t-manojkumar/ROBOTIC_ROVER/3D/Annotation ISO.png

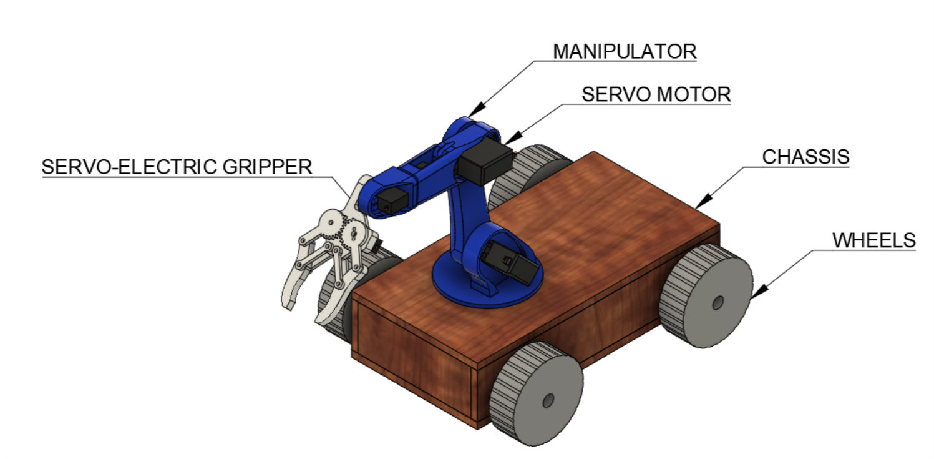
3D/Annotation ISO.png
