t-manojkumar/ROBOTIC_ROVER/3D/Annotation SIDE1.png

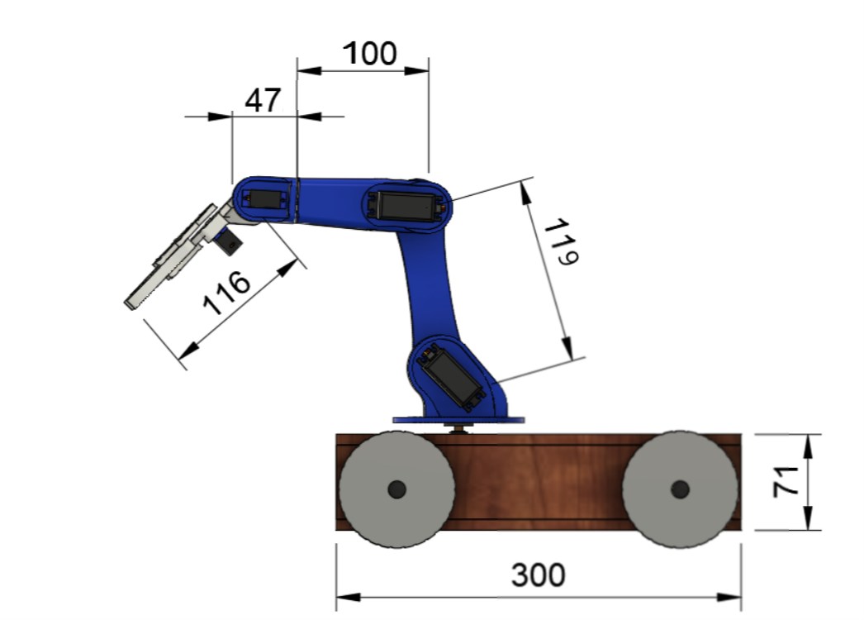
3D/Annotation SIDE1.png
