t-manojkumar/ROBOTIC_ROVER/3D/Annotation TOP.png

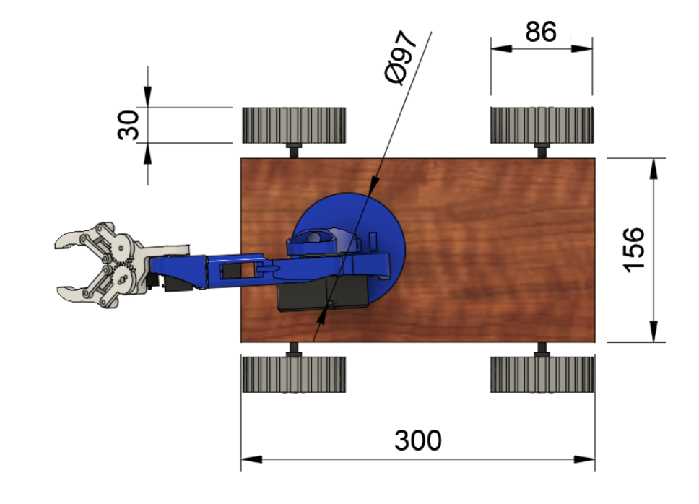
3D/Annotation TOP.png
