t-manojkumar/ROBOTIC_ROVER/CIRCUIT DIAGRAM/24d7c107-abdc-472a-8ade-f75f3b55037c.png

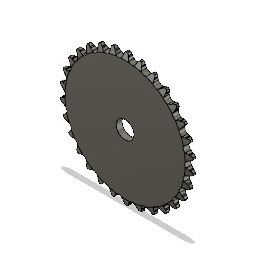
CIRCUIT DIAGRAM/24d7c107-abdc-472a-8ade-f75f3b55037c.png
