t-manojkumar/ROBOTIC_ROVER/CIRCUIT DIAGRAM/CIRCUIT.jpg

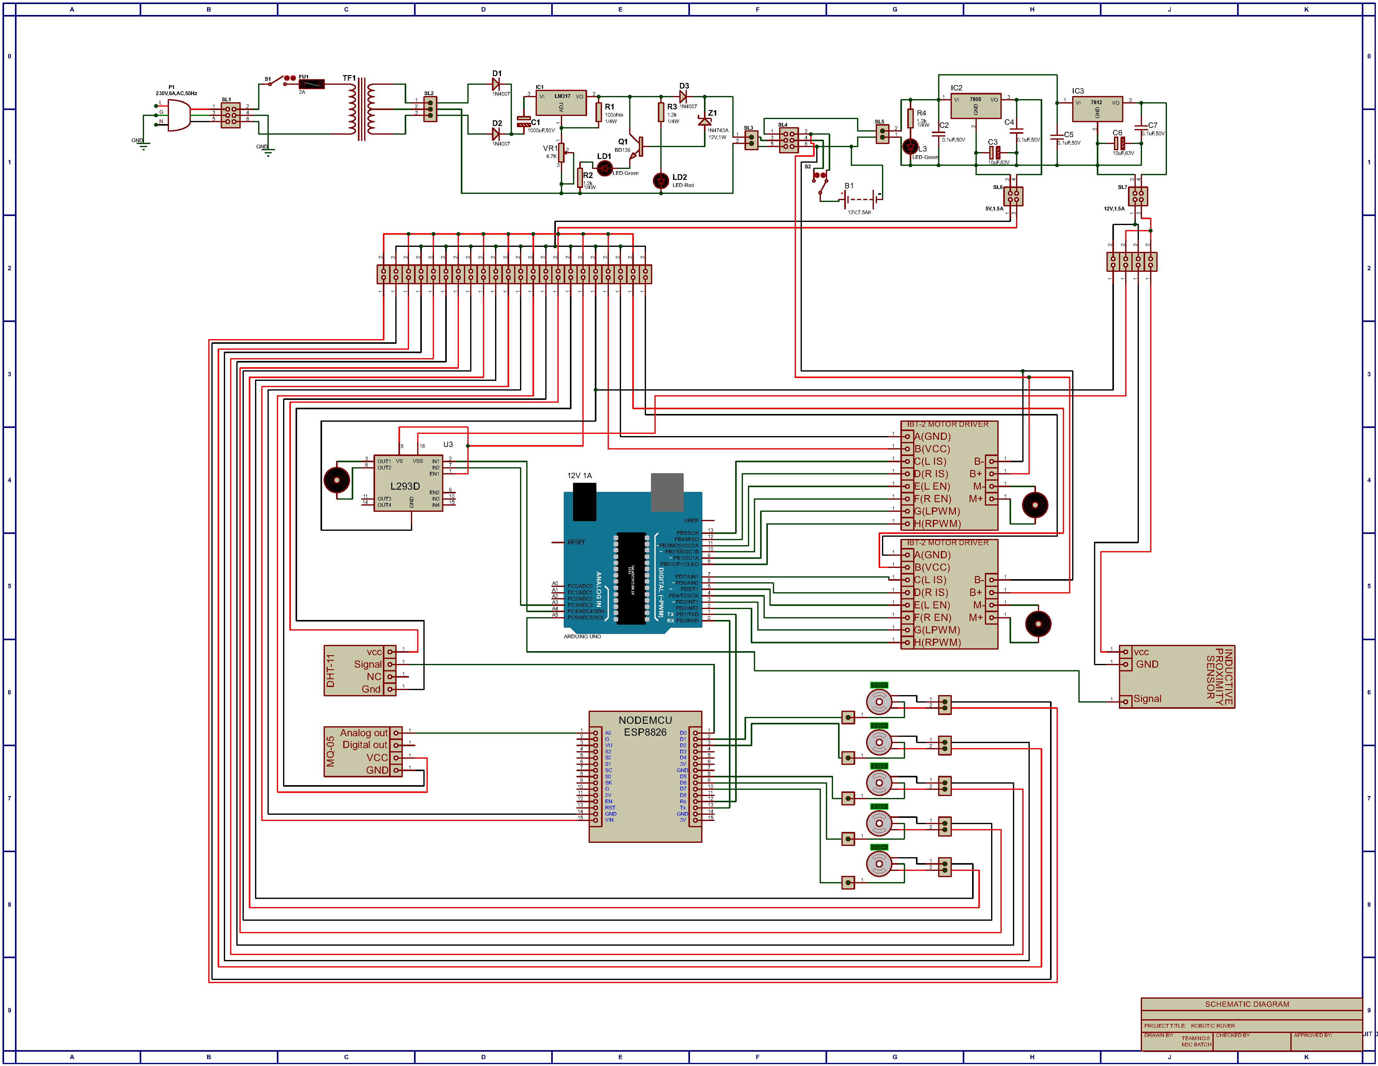
CIRCUIT DIAGRAM/CIRCUIT.jpg
