t-manojkumar/ROBOTIC_ROVER/MODULWISE/MODELWISE2.jpg

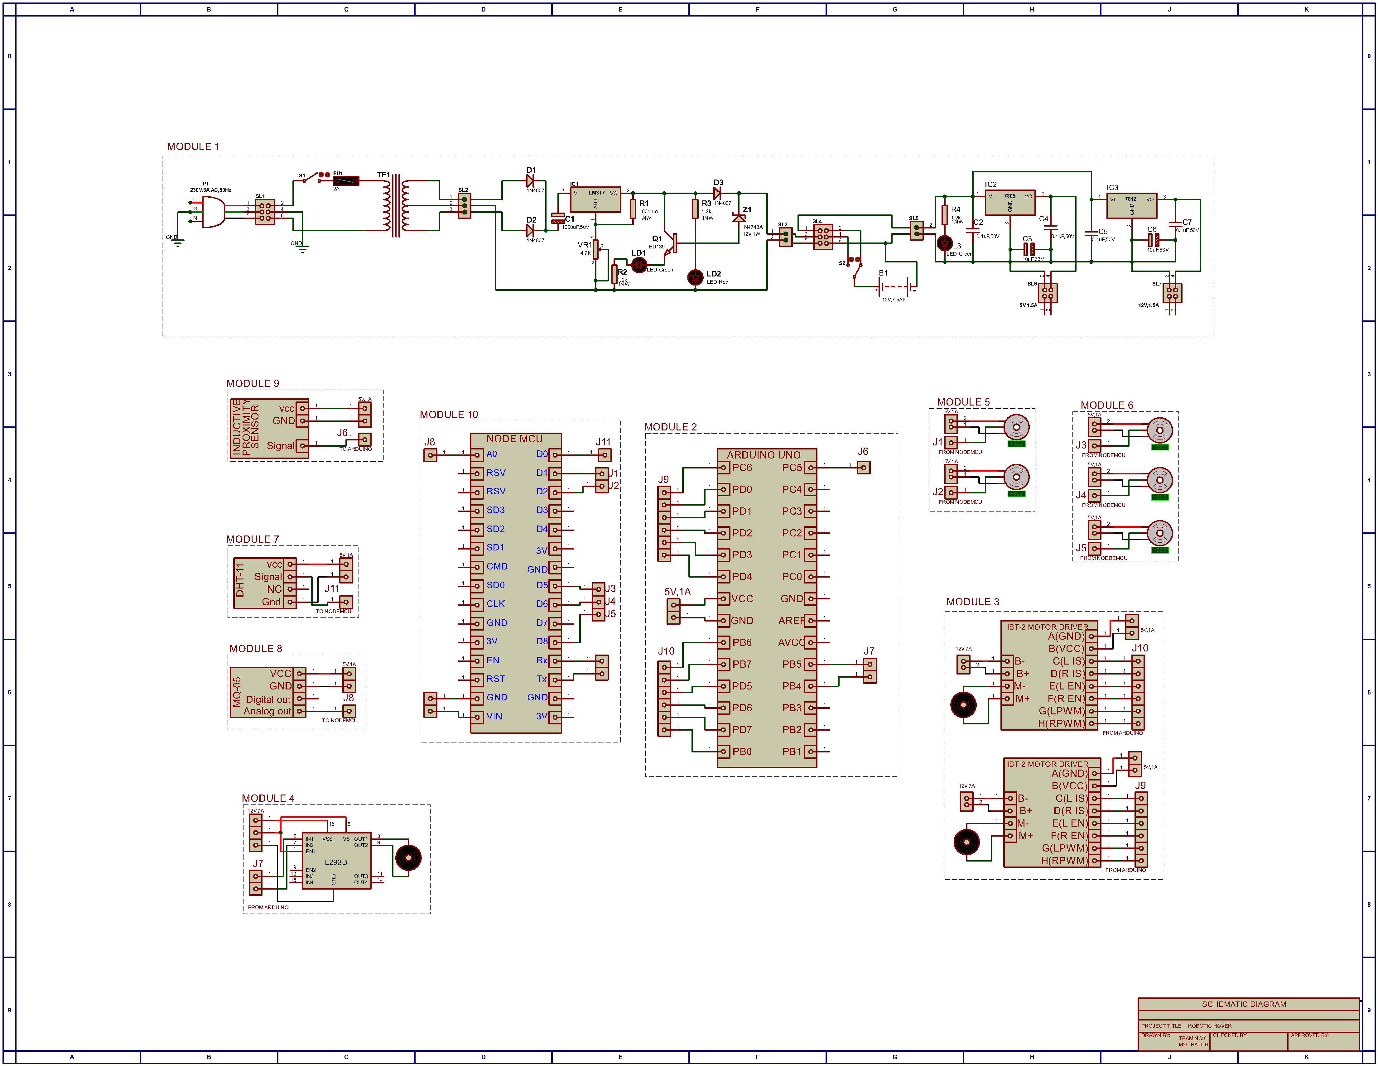
MODULWISE/MODELWISE2.jpg
