t-manojkumar/ROBOTIC_ROVER/MODULWISE/MODELWISE INTERCONNECTION.jpg

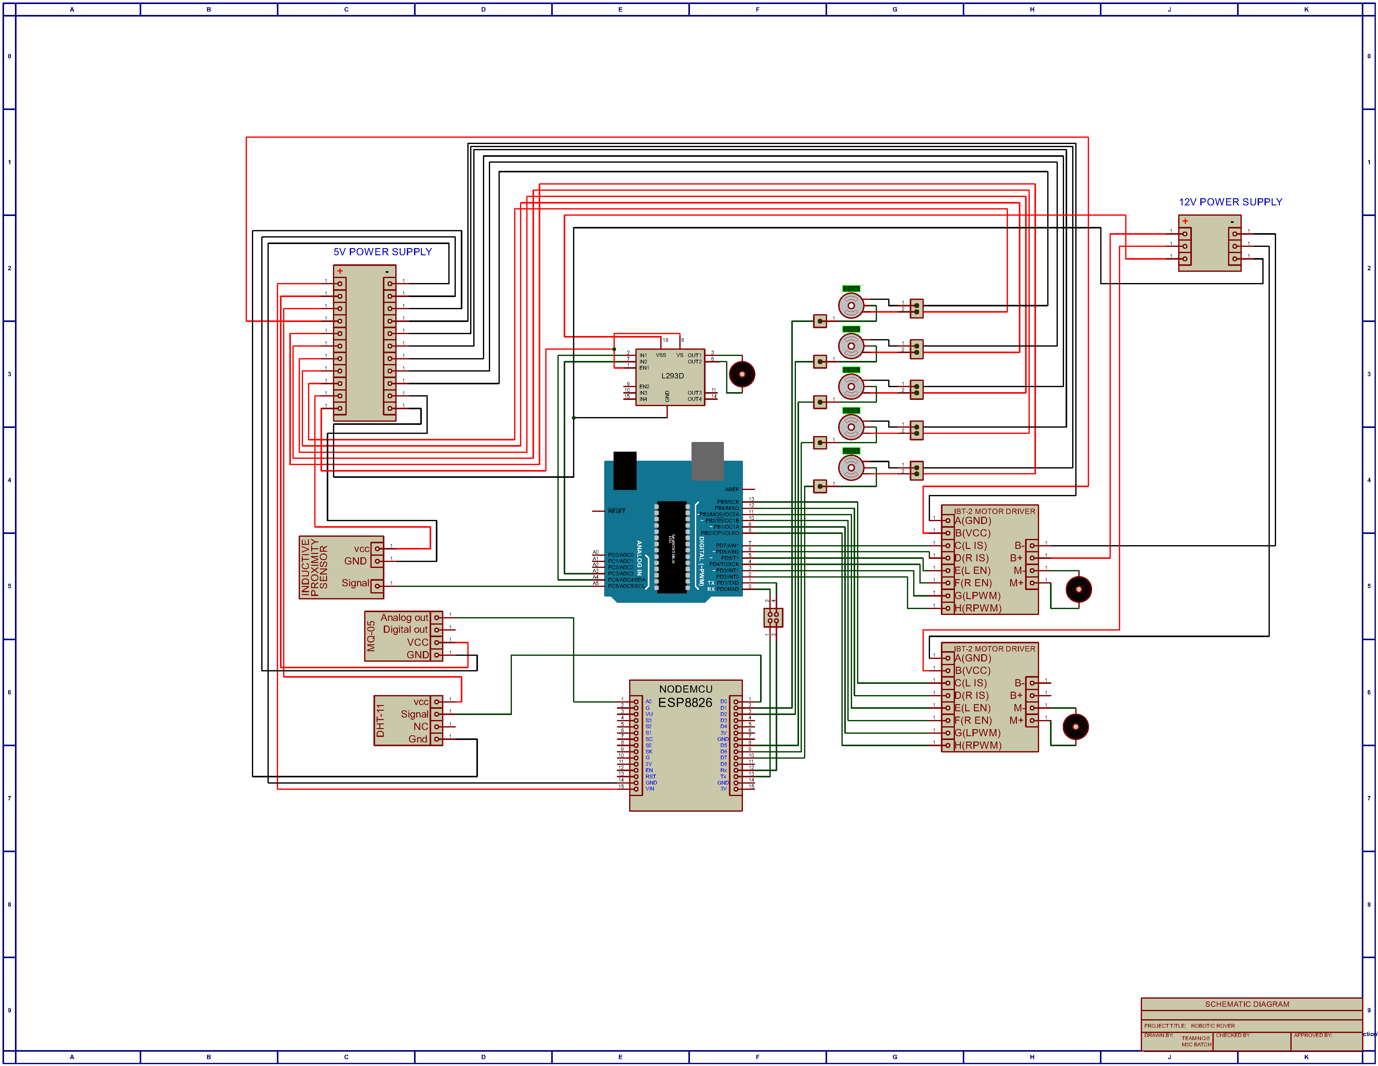
MODULWISE/MODELWISE INTERCONNECTION.jpg
